SachinKonan/DopplerLifeDetectionSystem/main/CancellationCode/CancelGraph2/F3d.png

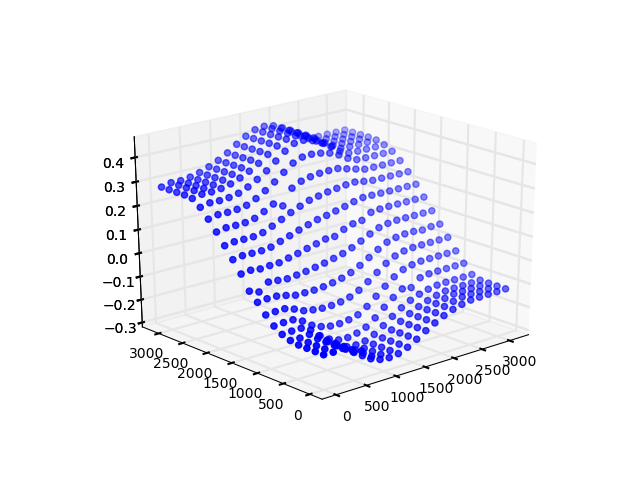
main/CancellationCode/CancelGraph2/F3d.png
