SachinKonan/DopplerLifeDetectionSystem/main/CancellationCode/CancelGraph2/phasepri.png

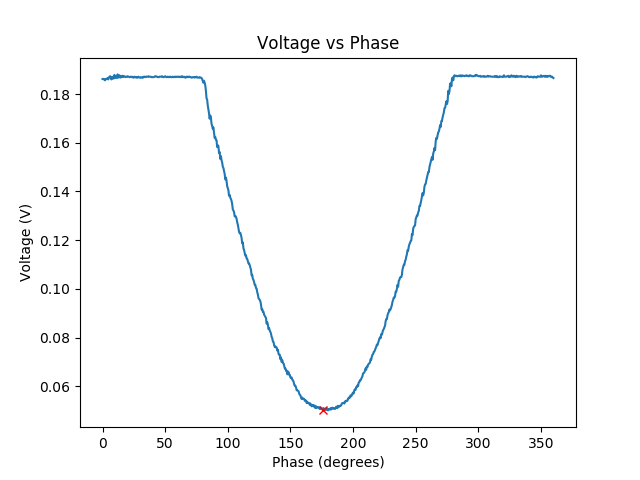
main/CancellationCode/CancelGraph2/phasepri.png
