SachinKonan/DopplerLifeDetectionSystem/main/CancellationCode/CancelGraph2/voltage.png

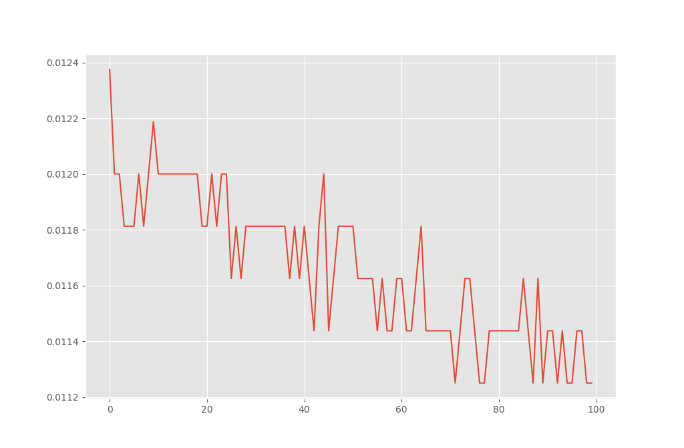
main/CancellationCode/CancelGraph2/voltage.png
