SachinKonan/DopplerLifeDetectionSystem/main/CancellationCode/CancelGraph2/voltampbrick.png

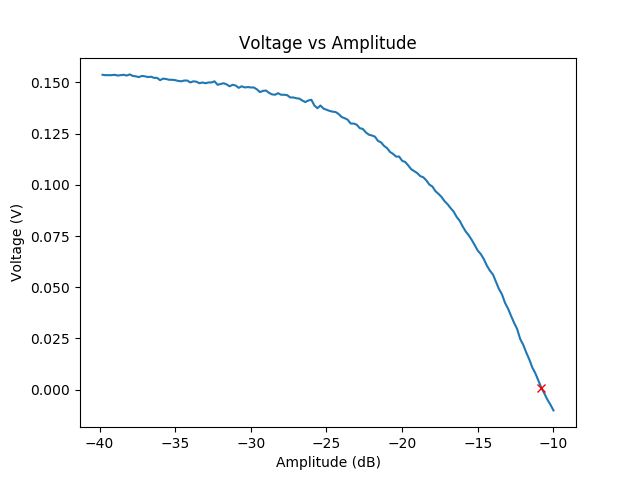
main/CancellationCode/CancelGraph2/voltampbrick.png
