SachinKonan/DopplerLifeDetectionSystem/main/CancellationCode/CancelGraph2/voltphastg.png

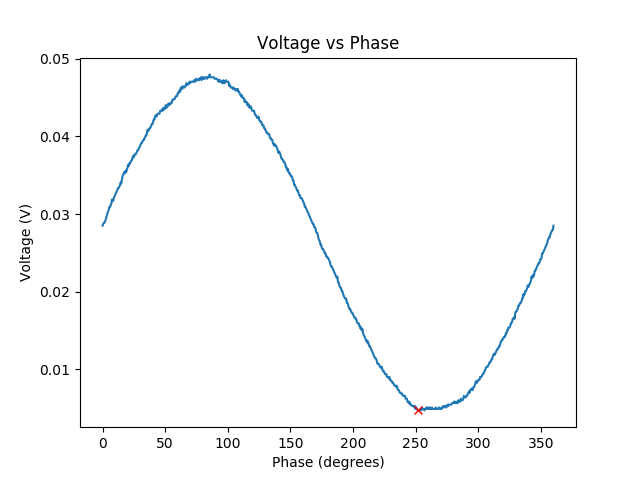
main/CancellationCode/CancelGraph2/voltphastg.png
