SachinKonan/DopplerLifeDetectionSystem/main/CancellationCode/CancelGraph2/voltvsamp3dB.png

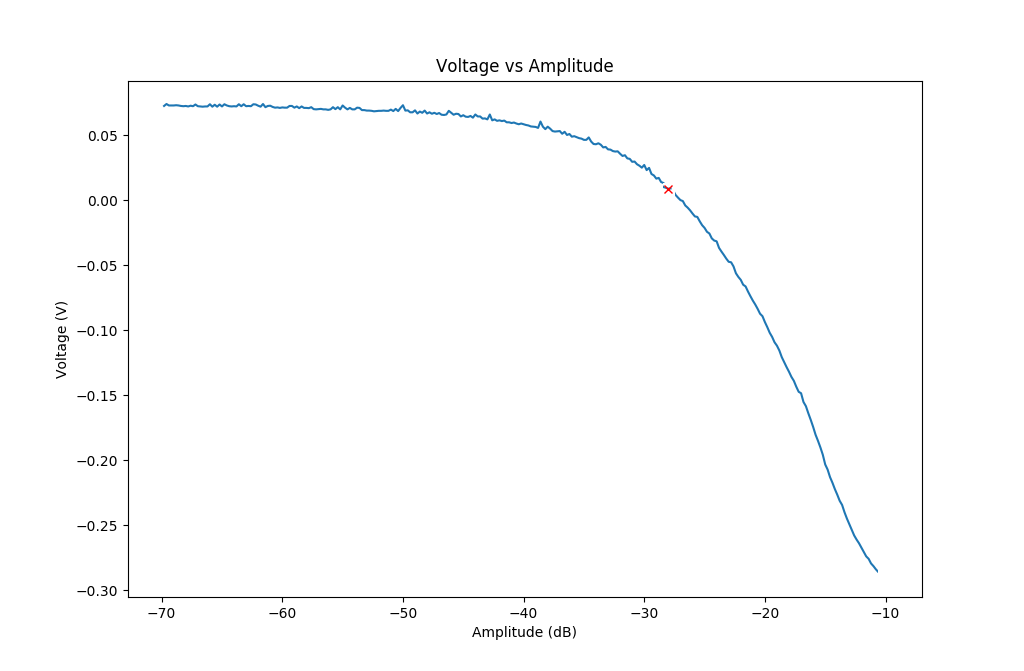
main/CancellationCode/CancelGraph2/voltvsamp3dB.png
