SachinKonan/DopplerLifeDetectionSystem/main/CancellationCode/CancelGraph2/voltvsamp30dB.png

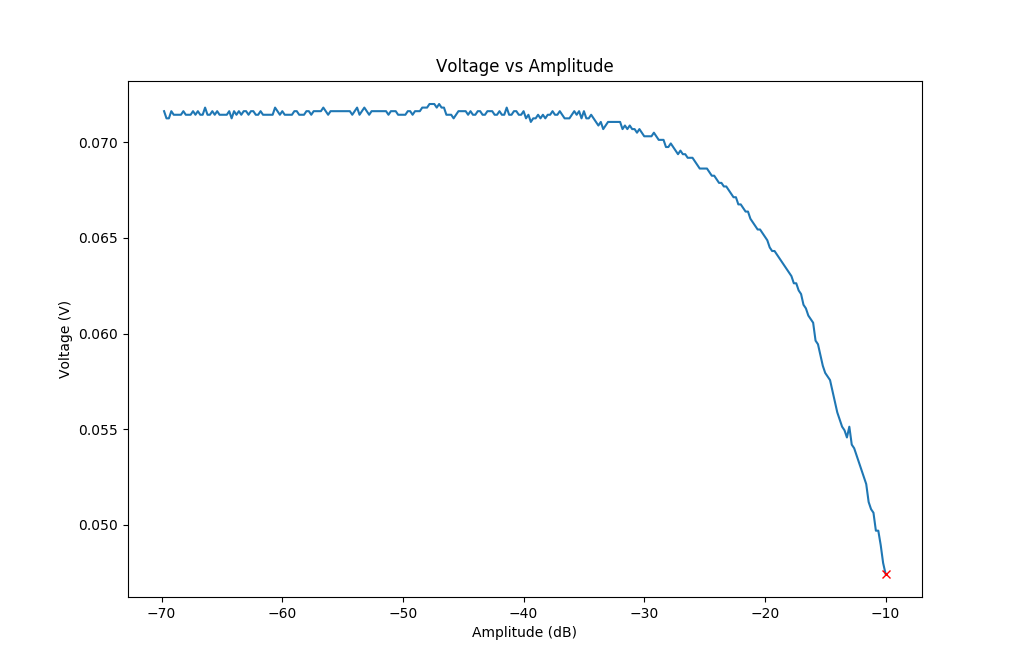
main/CancellationCode/CancelGraph2/voltvsamp30dB.png
