SachinKonan/DopplerLifeDetectionSystem/main/CancellationCode/CancelGraph2/voltvsamp130.png

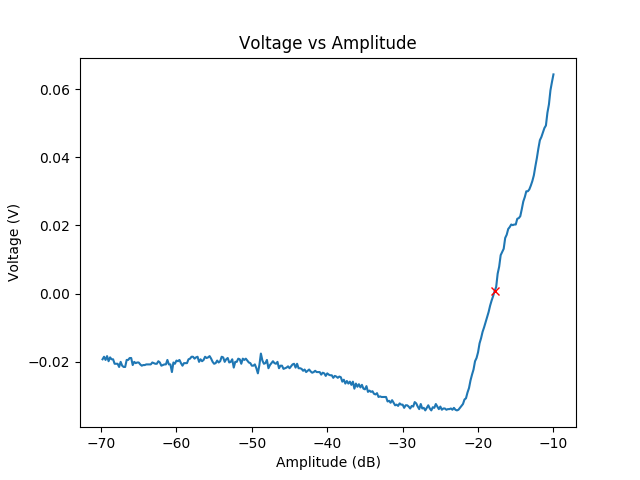
main/CancellationCode/CancelGraph2/voltvsamp130.png
