SachinKonan/DopplerLifeDetectionSystem/main/CancellationCode/CancelGraph2/voltvsampconcrete1.png

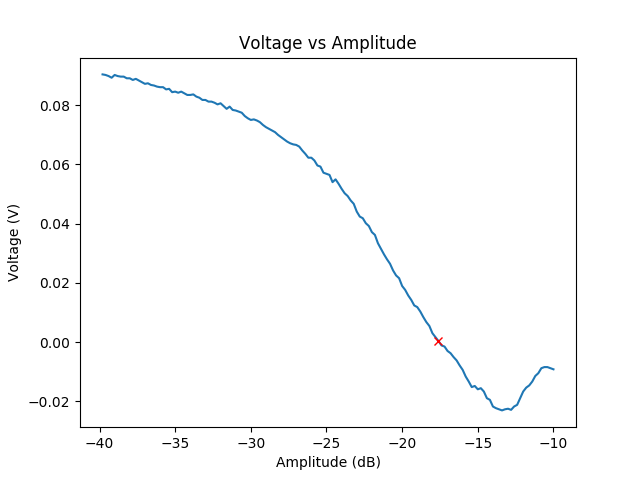
main/CancellationCode/CancelGraph2/voltvsampconcrete1.png
