SachinKonan/DopplerLifeDetectionSystem/main/CancellationCode/CancelGraph2/voltvsampnotten.png

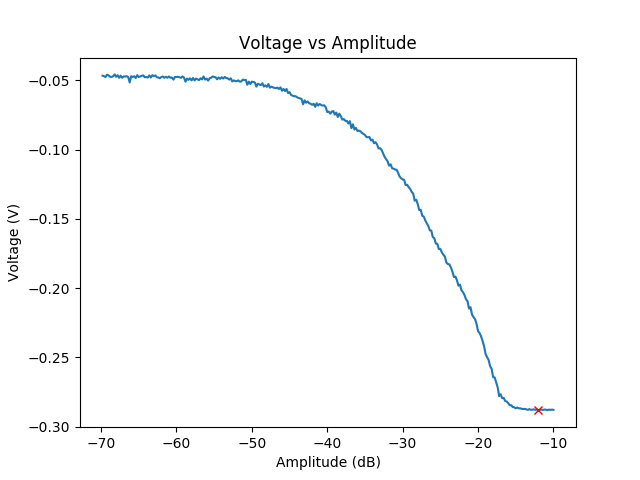
main/CancellationCode/CancelGraph2/voltvsampnotten.png
