SachinKonan/DopplerLifeDetectionSystem/main/CancellationCode/CancelGraph2/voltvsphase3dB.png

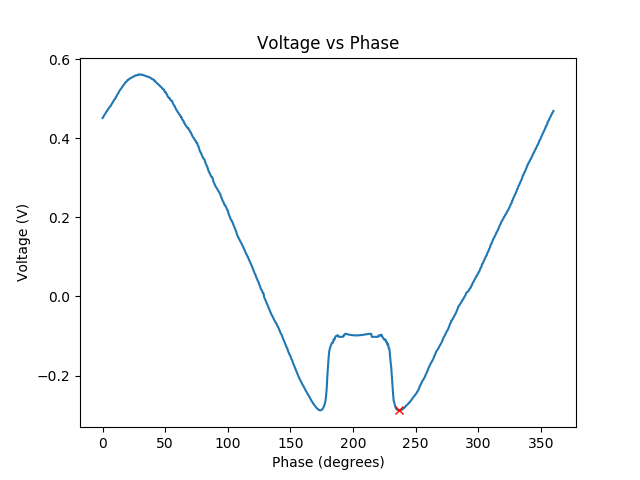
main/CancellationCode/CancelGraph2/voltvsphase3dB.png
