SachinKonan/DopplerLifeDetectionSystem/main/CancellationCode/CancelGraph2/voltvsphase30dB.png

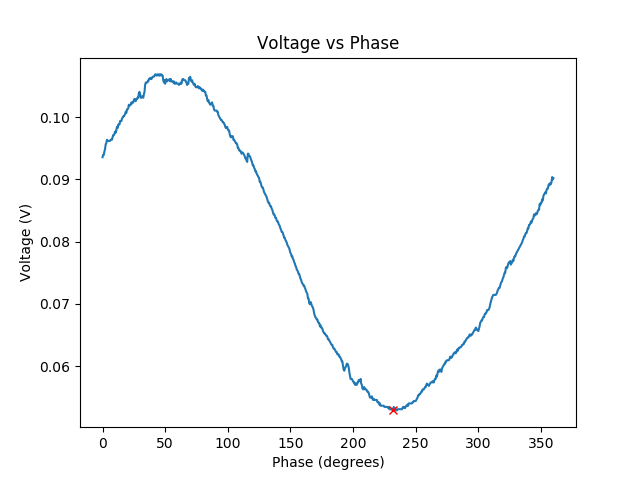
main/CancellationCode/CancelGraph2/voltvsphase30dB.png
