SachinKonan/DopplerLifeDetectionSystem/main/CancellationCode/CancelGraph2/voltvsphase130.png

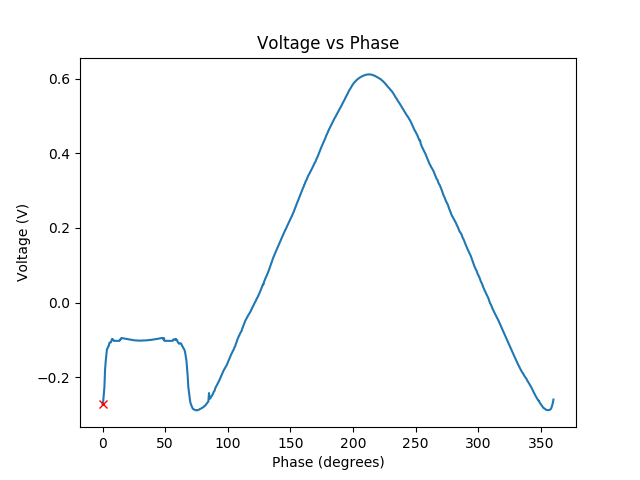
main/CancellationCode/CancelGraph2/voltvsphase130.png
