SachinKonan/DopplerLifeDetectionSystem/main/CancellationCode/CancelGraph2/voltvsphaseconcrete1.png

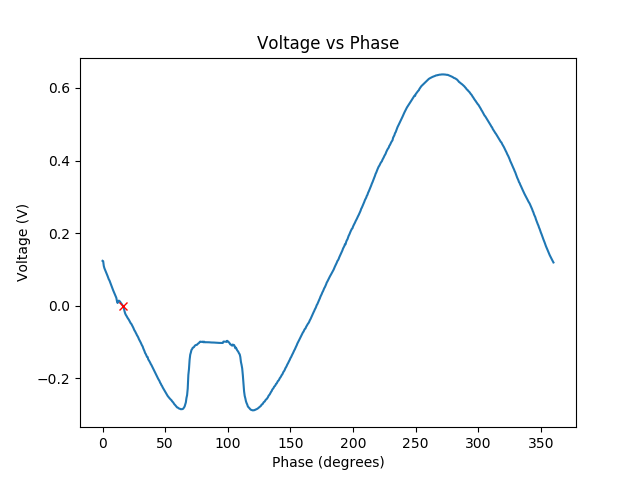
main/CancellationCode/CancelGraph2/voltvsphaseconcrete1.png
