SachinKonan/DopplerLifeDetectionSystem/main/CancellationCode/CancelGraph2/voltvsphasenoatten.png

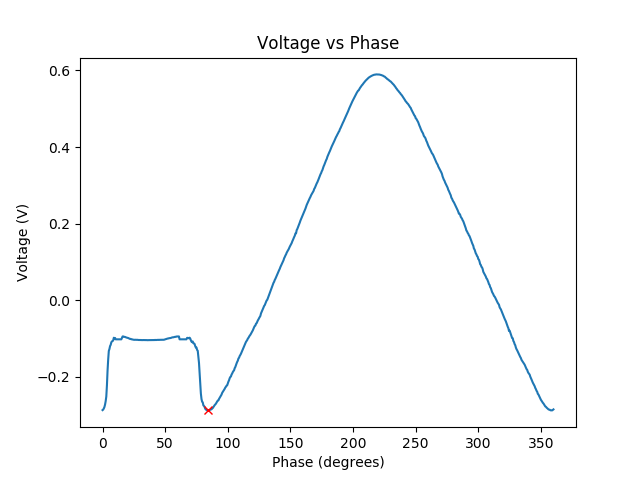
main/CancellationCode/CancelGraph2/voltvsphasenoatten.png
