SachinKonan/DopplerLifeDetectionSystem/main/CancellationCode/phasecalib.png

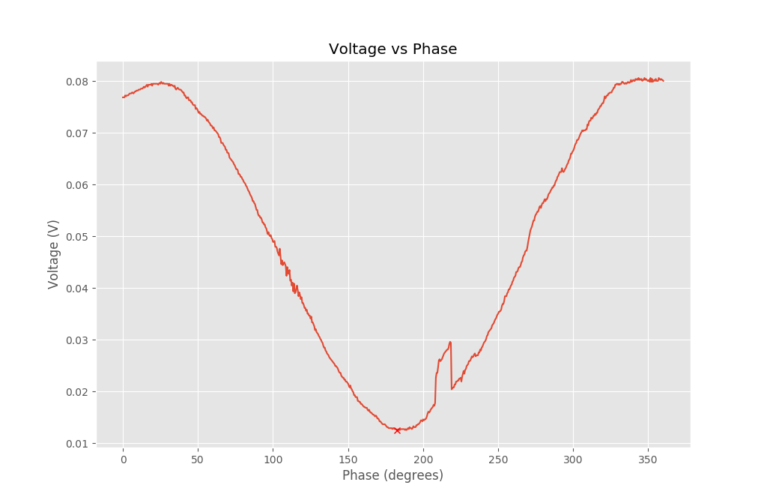
main/CancellationCode/phasecalib.png
