SachinKonan/DopplerLifeDetectionSystem/main/SimpleOscilloscope/RPIVisulaization.png

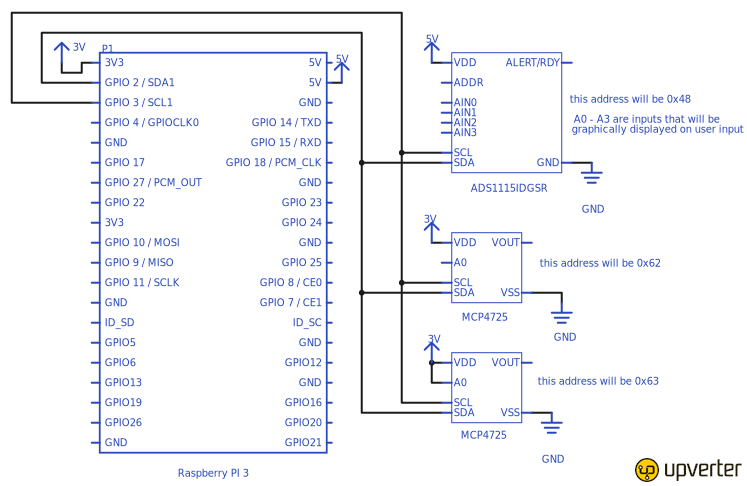
main/SimpleOscilloscope/RPIVisulaization.png
