SachinKonan/DopplerLifeDetectionSystem/PCBRadar/radarpcb3D.png

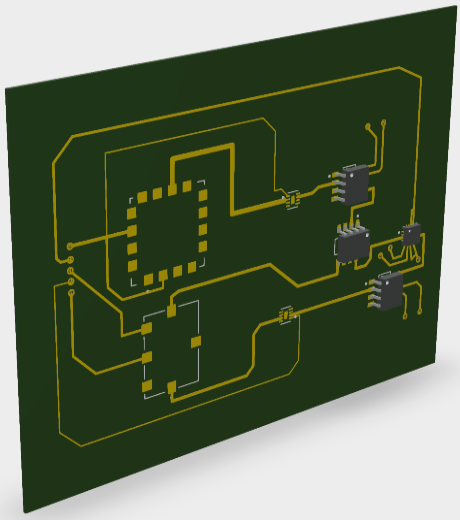
PCBRadar/radarpcb3D.png
