SachinKonan/DopplerLifeDetectionSystem/PCBRadar/radarpcb.PNG

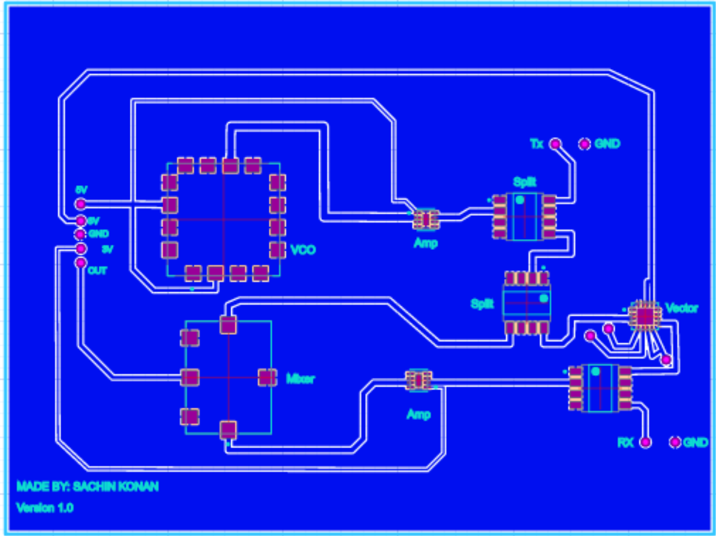
PCBRadar/radarpcb.PNG
