SachinKonan/DopplerLifeDetectionSystem/RadarFull/antennaplacement.png

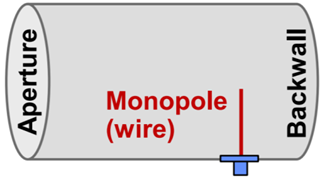
RadarFull/antennaplacement.png
