SachinKonan/DopplerLifeDetectionSystem/RadarFull/filter.amplifier.circuit.png

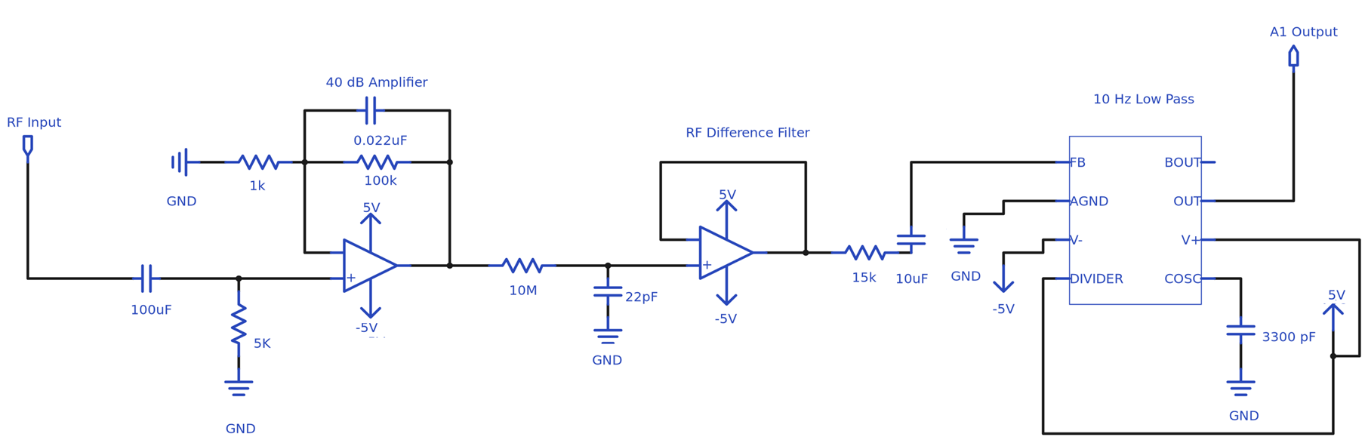
RadarFull/filter.amplifier.circuit.png
