SachinKonan/DopplerLifeDetectionSystem/RadarFull/powersupply.png

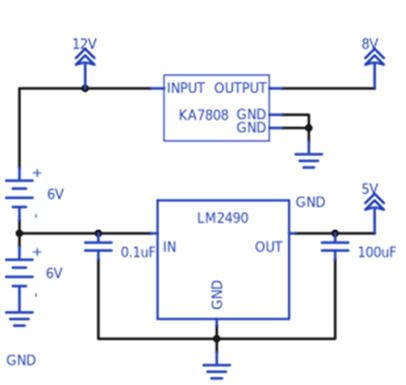
RadarFull/powersupply.png
