SachinKonan/DopplerLifeDetectionSystem/RadarFull/radarfull.png

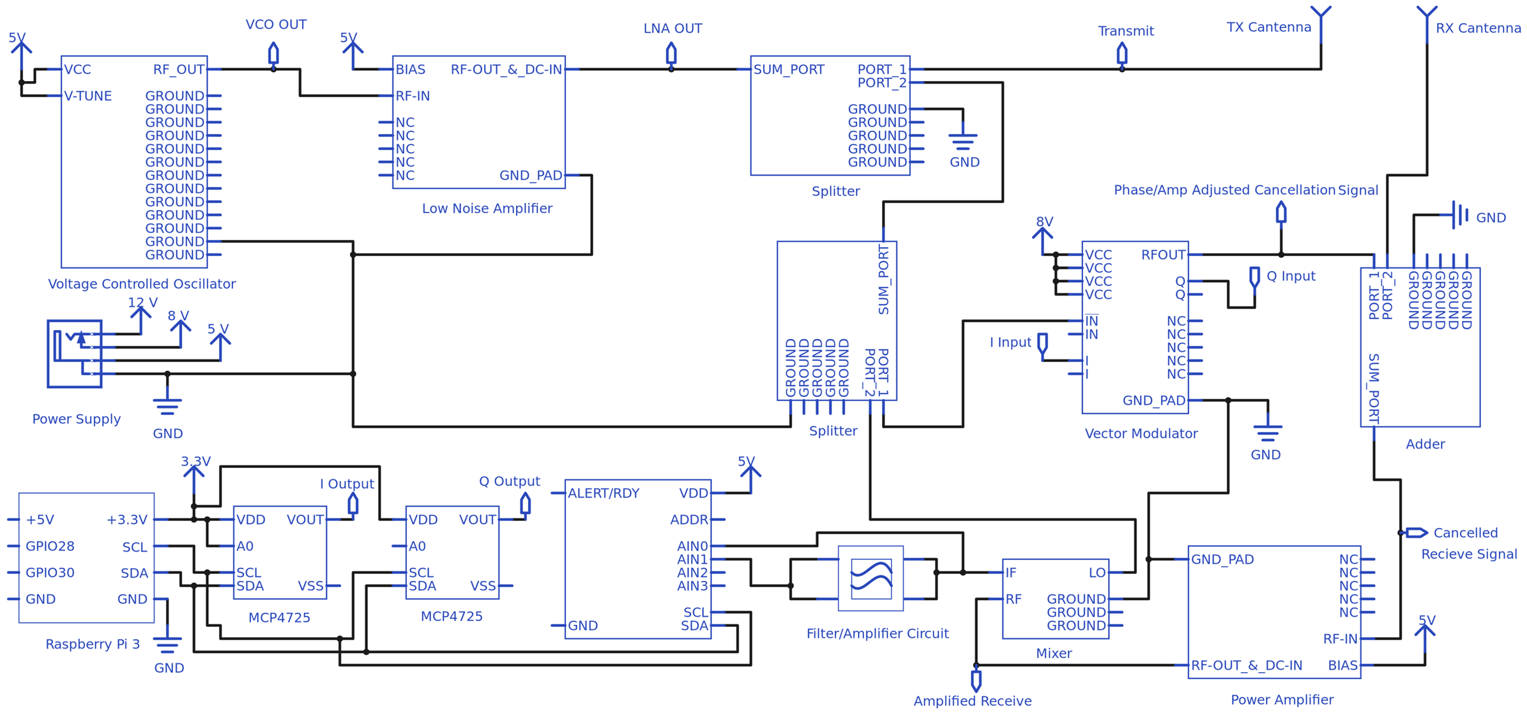
RadarFull/radarfull.png
