SachinKonan/DopplerLifeDetectionSystem/main/CancellationCode/CalibrationGraphs/control.png

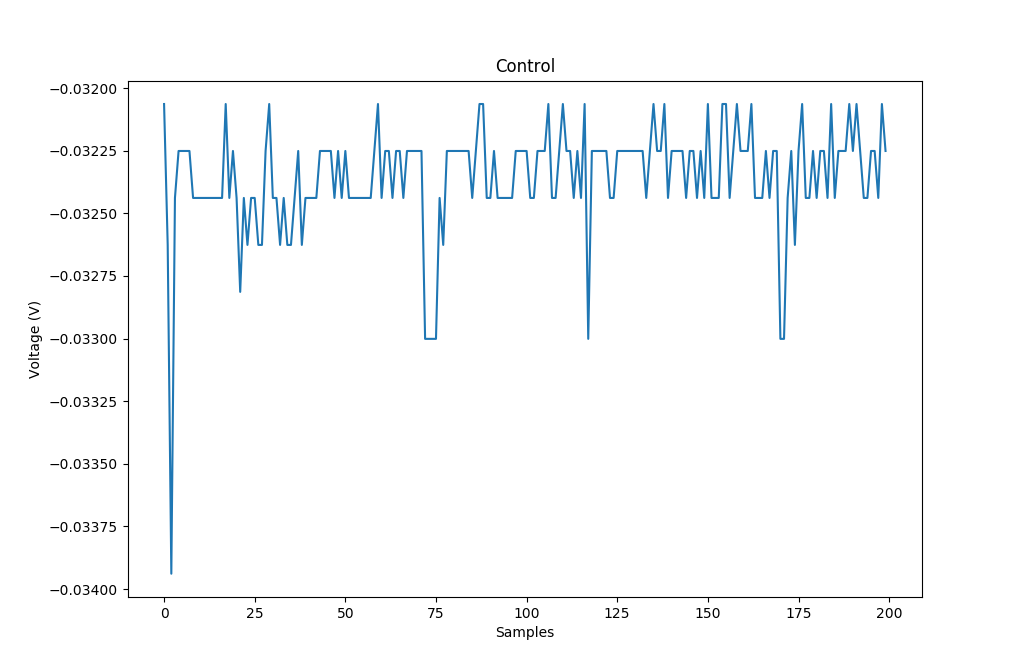
main/CancellationCode/CalibrationGraphs/control.png
