SachinKonan/DopplerLifeDetectionSystem/main/CancellationCode/CalibrationGraphs/voltvsamp1.png

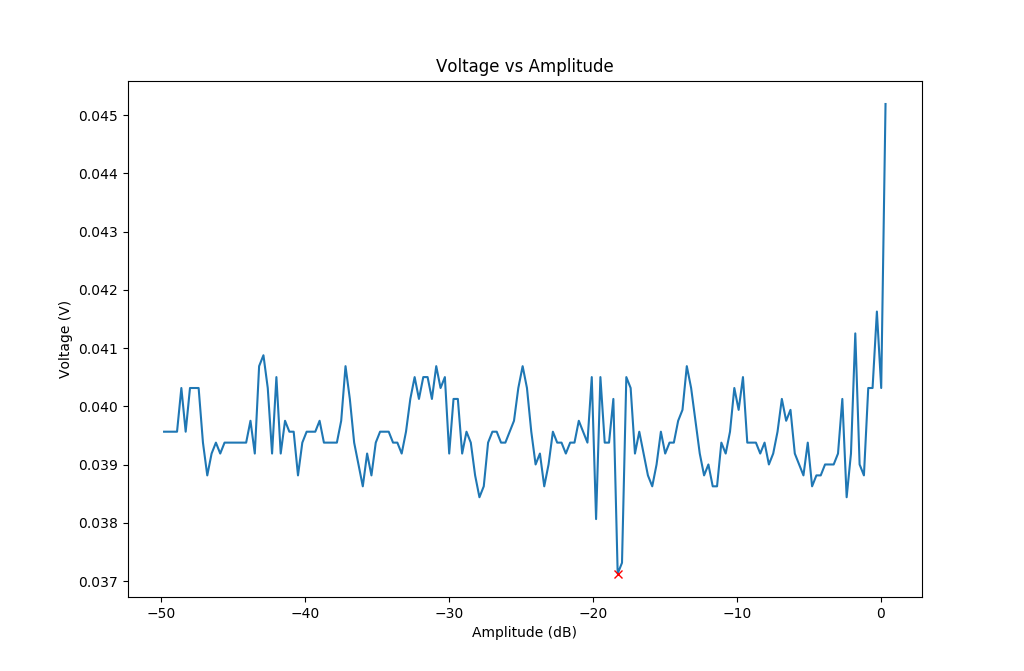
main/CancellationCode/CalibrationGraphs/voltvsamp1.png
