SachinKonan/DopplerLifeDetectionSystem/main/CancellationCode/CalibrationGraphs/voltvsamp2.png

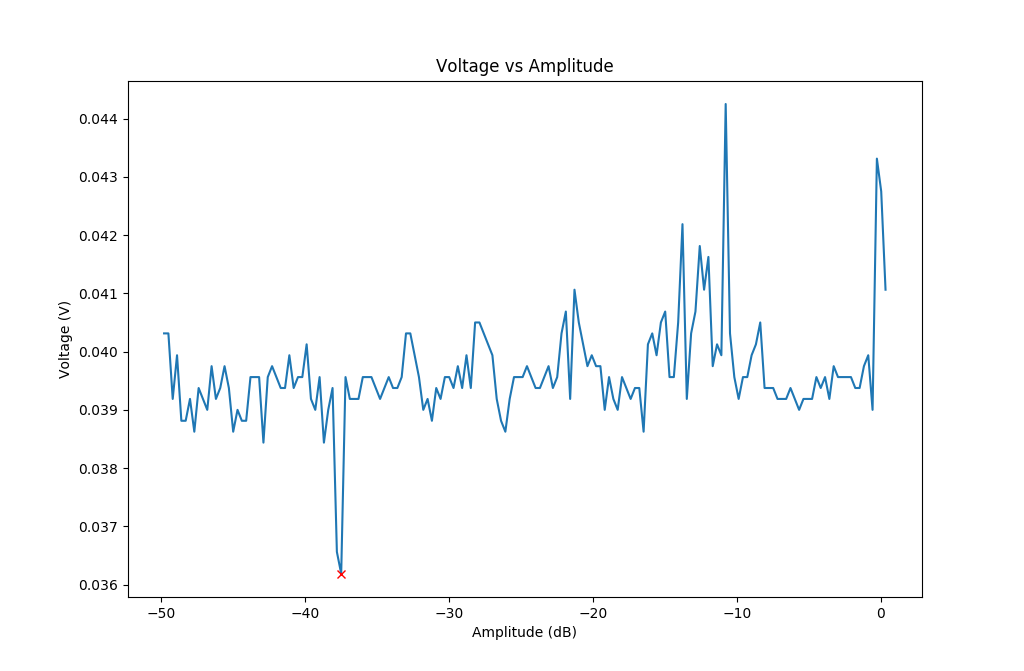
main/CancellationCode/CalibrationGraphs/voltvsamp2.png
