SachinKonan/DopplerLifeDetectionSystem/main/CancellationCode/CalibrationGraphs/voltvsamp3.png

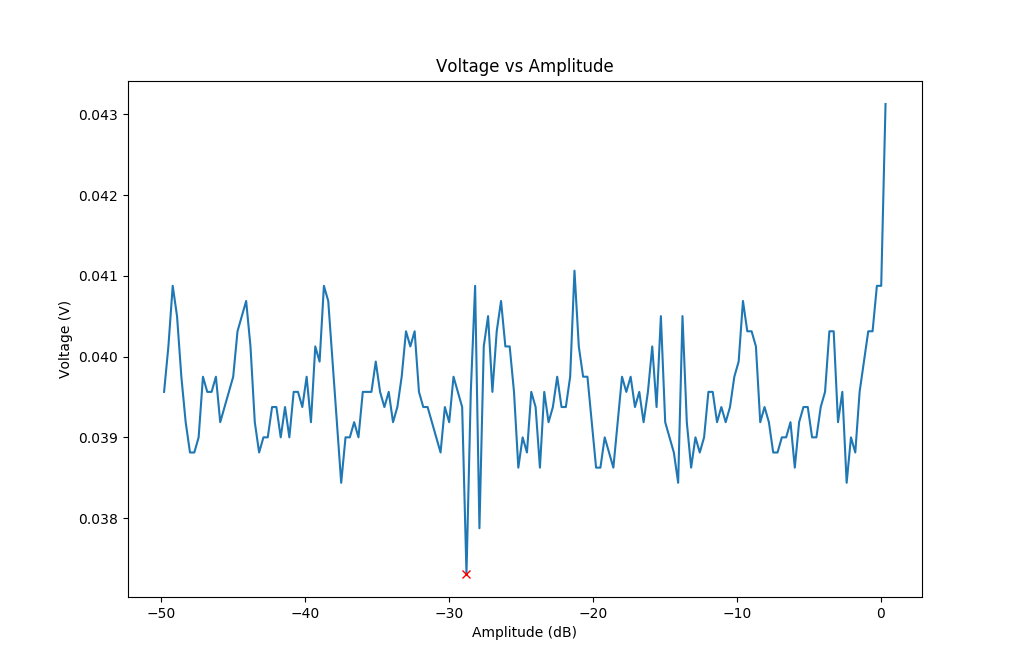
main/CancellationCode/CalibrationGraphs/voltvsamp3.png
