SachinKonan/DopplerLifeDetectionSystem/main/CancellationCode/CalibrationGraphs/voltvsamp4.png

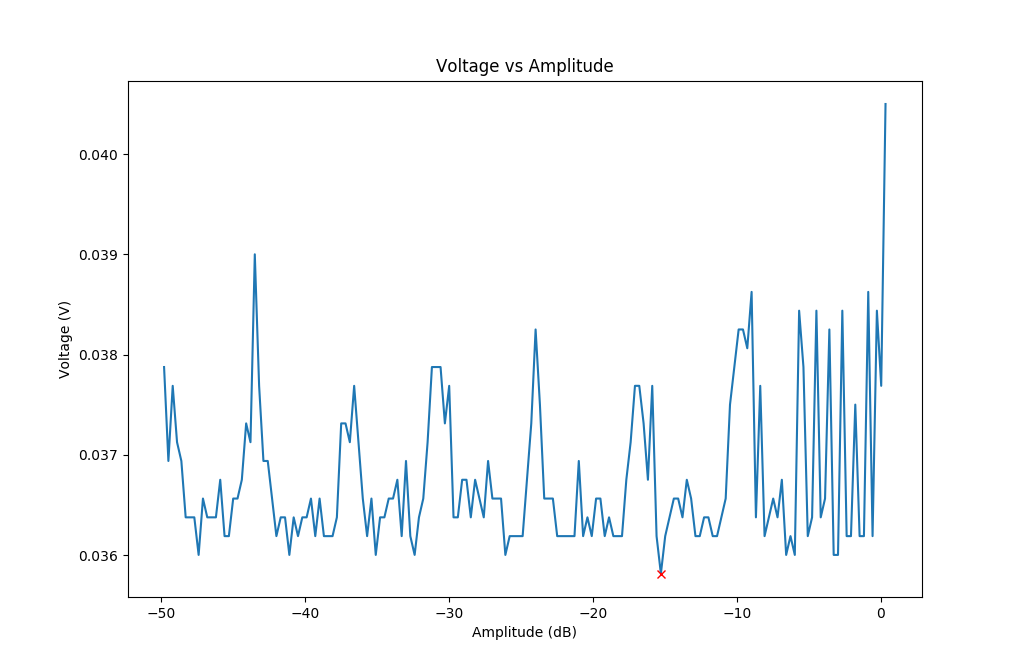
main/CancellationCode/CalibrationGraphs/voltvsamp4.png
