SachinKonan/DopplerLifeDetectionSystem/main/CancellationCode/CalibrationGraphs/voltvsamp5.png

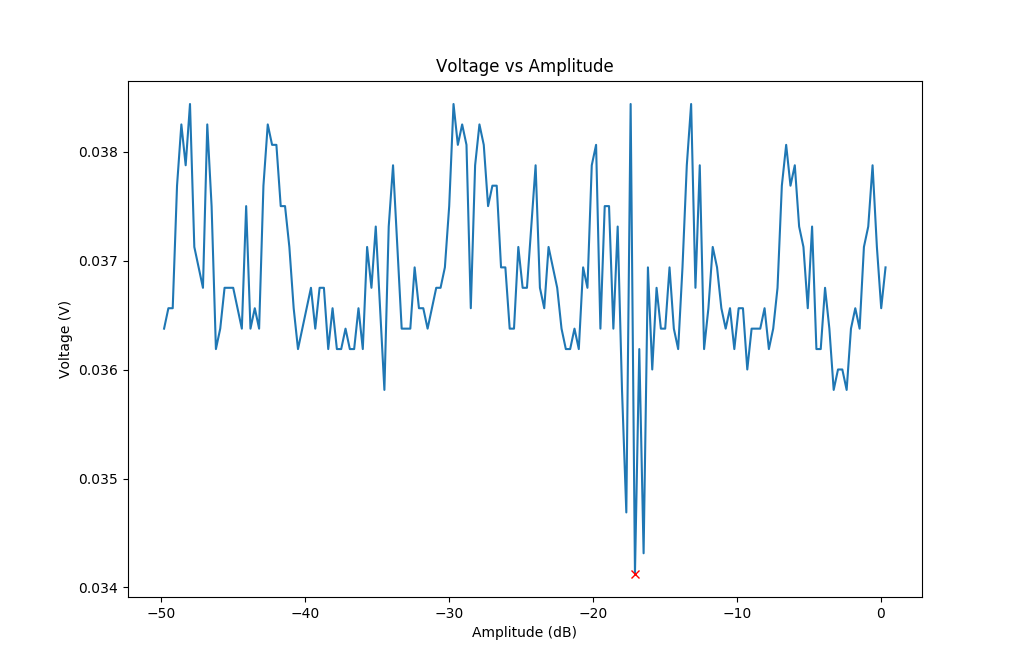
main/CancellationCode/CalibrationGraphs/voltvsamp5.png
