SachinKonan/DopplerLifeDetectionSystem/main/CancellationCode/CalibrationGraphs/voltvsamp.png

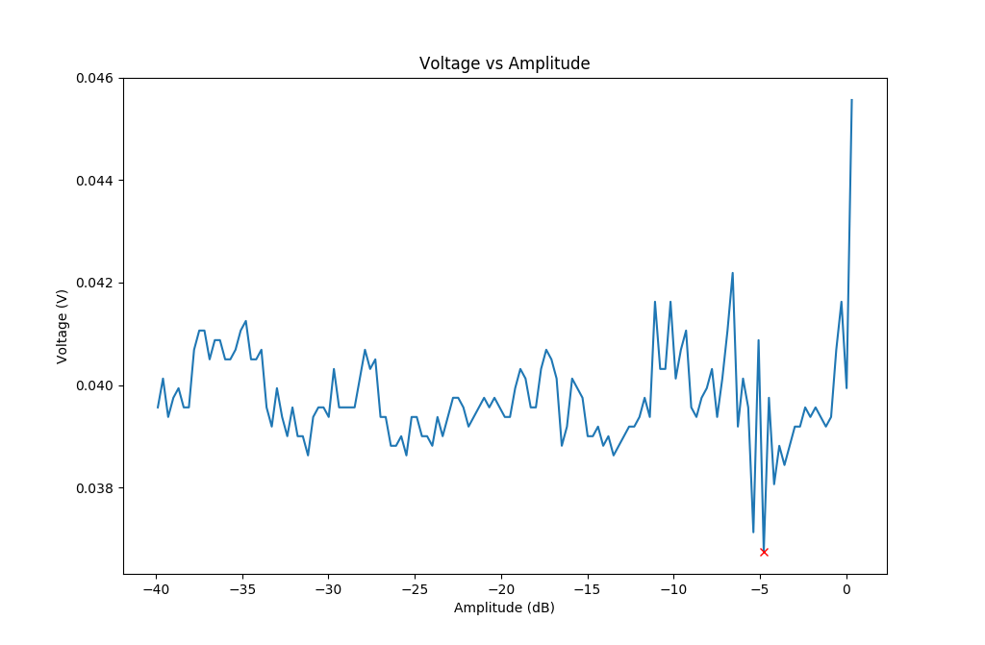
main/CancellationCode/CalibrationGraphs/voltvsamp.png
