SachinKonan/DopplerLifeDetectionSystem/main/CancellationCode/CalibrationGraphs/voltvsamprevisedphase.png

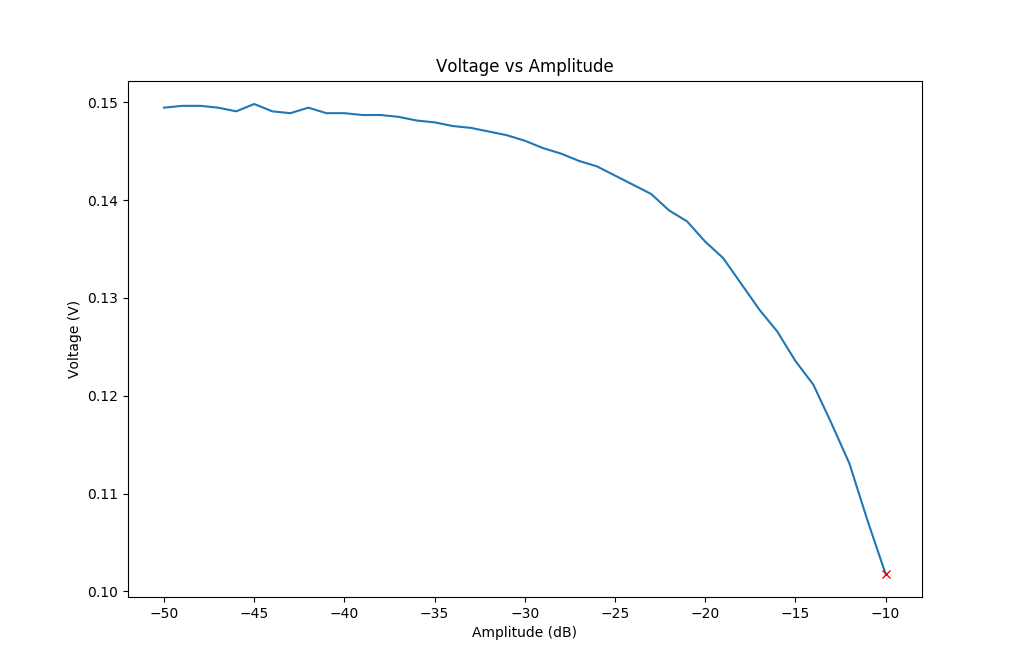
main/CancellationCode/CalibrationGraphs/voltvsamprevisedphase.png
