SachinKonan/DopplerLifeDetectionSystem/main/CancellationCode/CalibrationGraphs/voltvsphase1.png

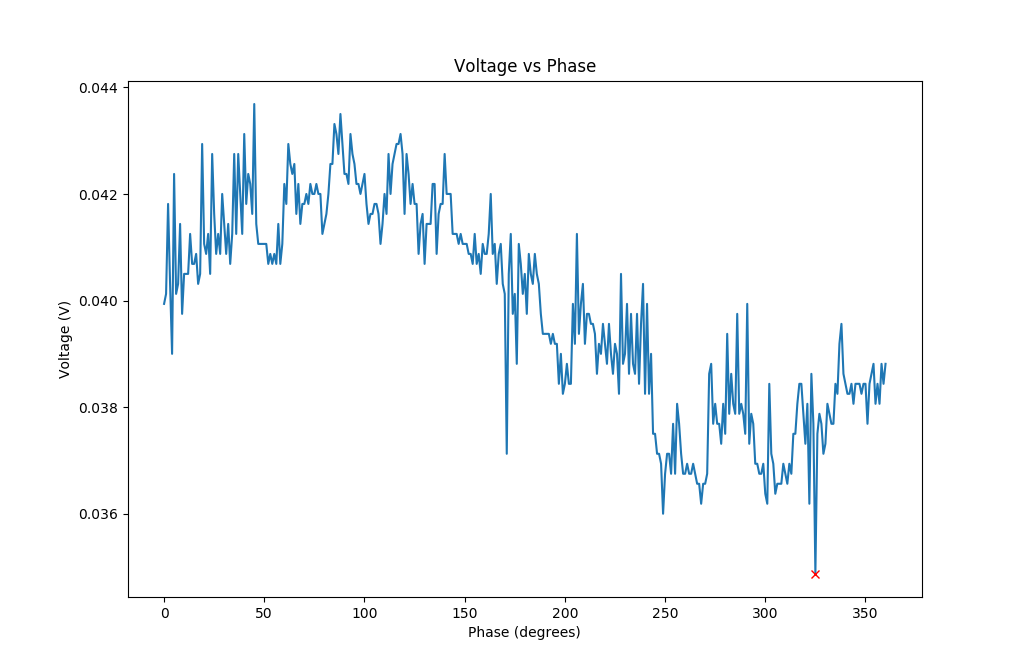
main/CancellationCode/CalibrationGraphs/voltvsphase1.png
