SachinKonan/DopplerLifeDetectionSystem/main/CancellationCode/CalibrationGraphs/voltvsphase2.png

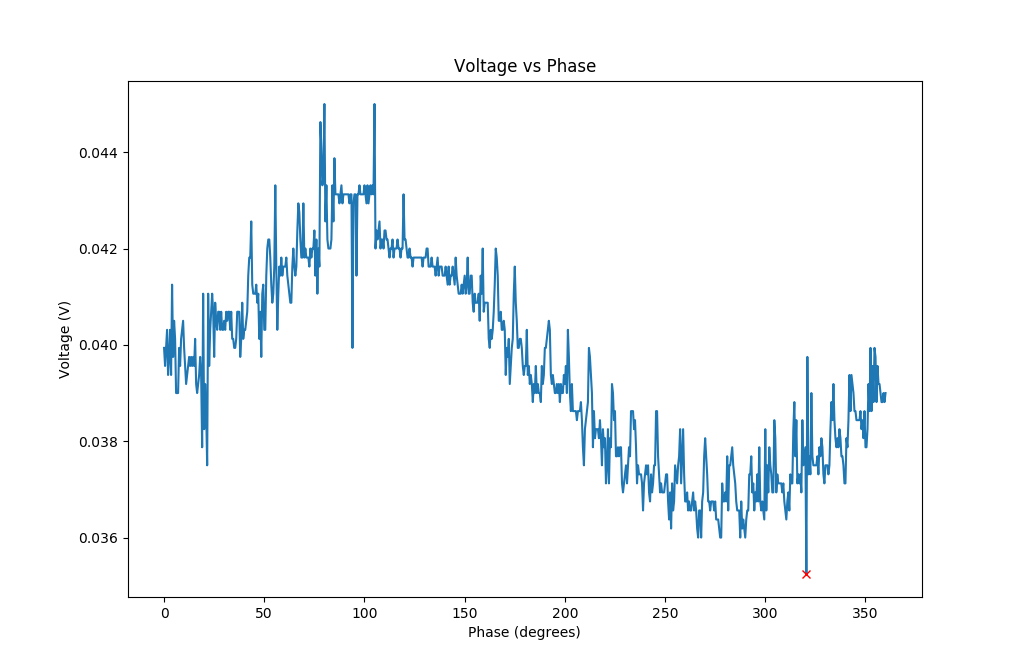
main/CancellationCode/CalibrationGraphs/voltvsphase2.png
