SachinKonan/DopplerLifeDetectionSystem/main/CancellationCode/CalibrationGraphs/voltvsphase3.png

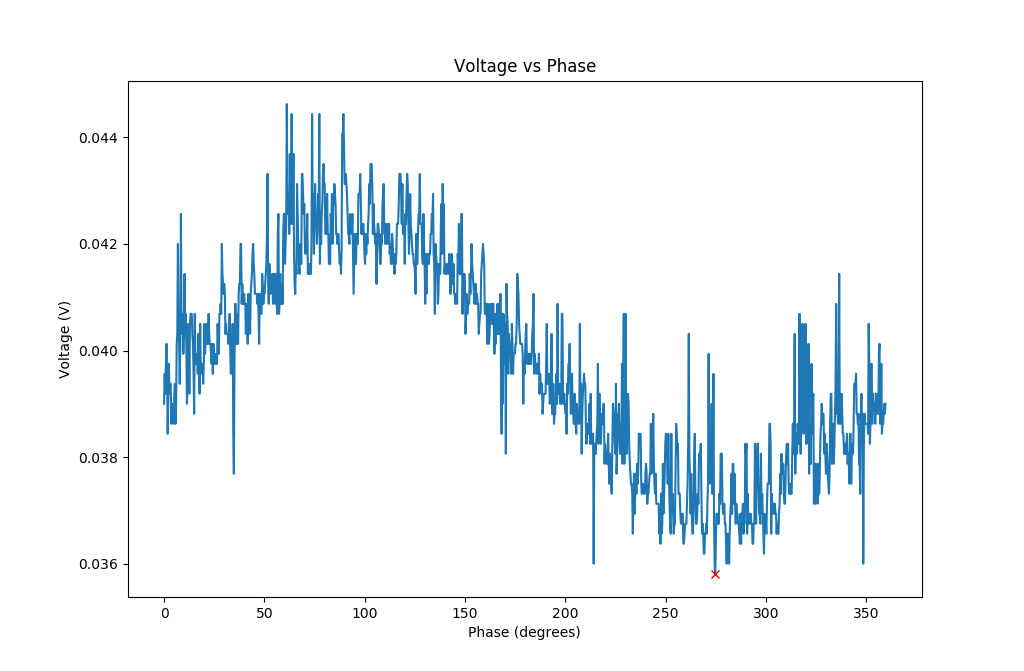
main/CancellationCode/CalibrationGraphs/voltvsphase3.png
