SachinKonan/DopplerLifeDetectionSystem/main/CancellationCode/CalibrationGraphs/voltvsphase7.png

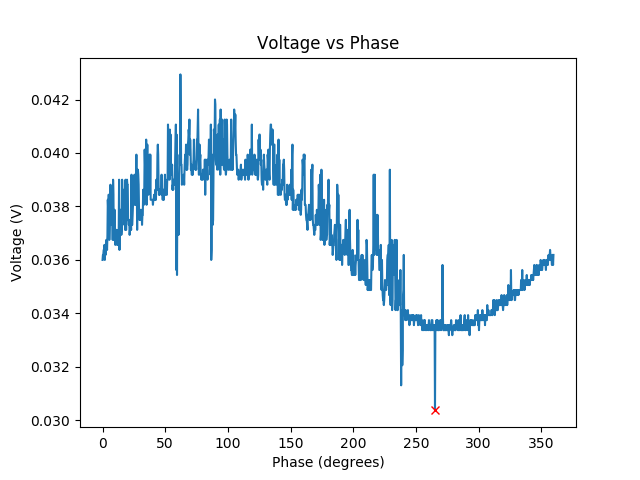
main/CancellationCode/CalibrationGraphs/voltvsphase7.png
