SachinKonan/DopplerLifeDetectionSystem/main/CancellationCode/CalibrationGraphs/voltvsphase8.png

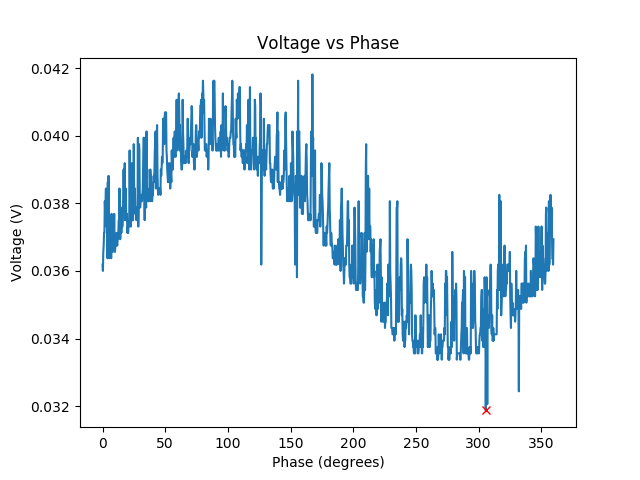
main/CancellationCode/CalibrationGraphs/voltvsphase8.png
