SachinKonan/DopplerLifeDetectionSystem/main/CancellationCode/CalibrationGraphs/voltvsphase720.png

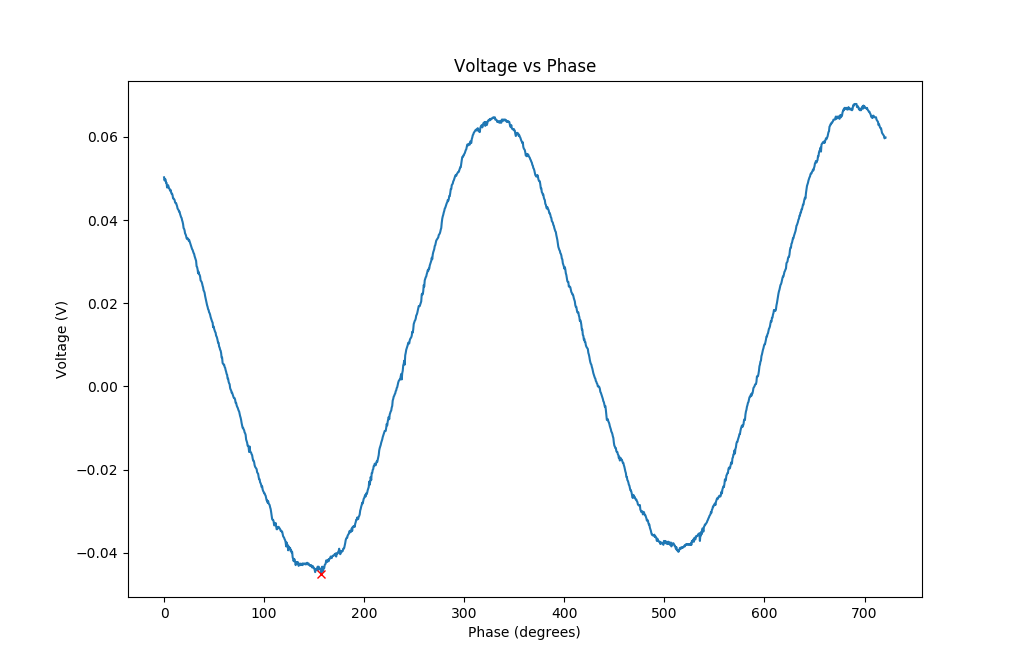
main/CancellationCode/CalibrationGraphs/voltvsphase720.png
