SachinKonan/DopplerLifeDetectionSystem/main/CancellationCode/CalibrationGraphs/voltvsphaserevised1.png

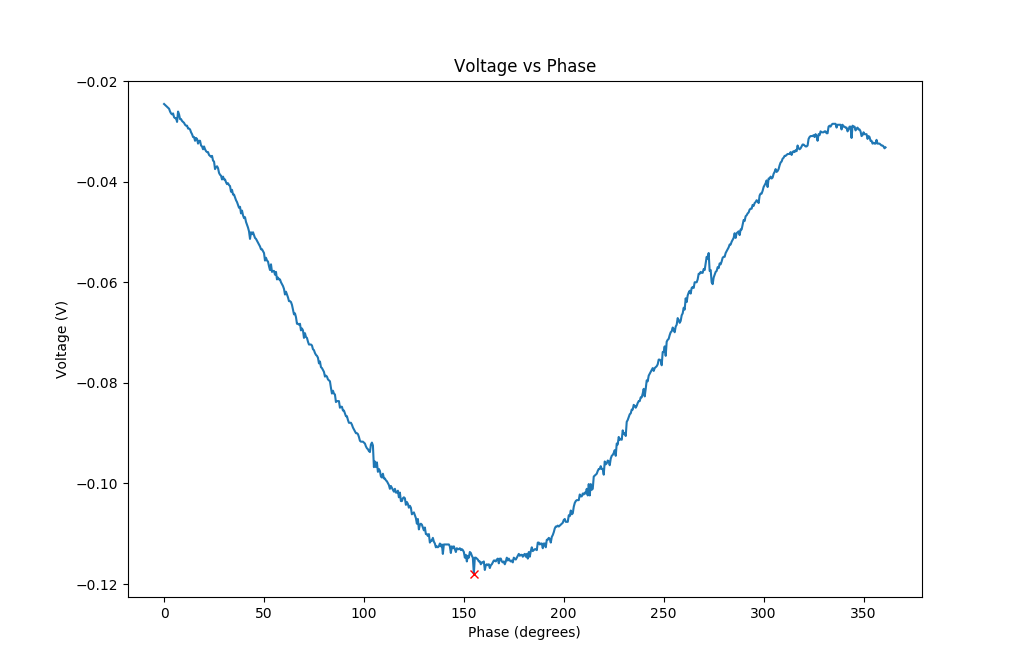
main/CancellationCode/CalibrationGraphs/voltvsphaserevised1.png
