SachinKonan/DopplerLifeDetectionSystem/main/CancellationCode/CalibrationGraphs/voltvsratio.png

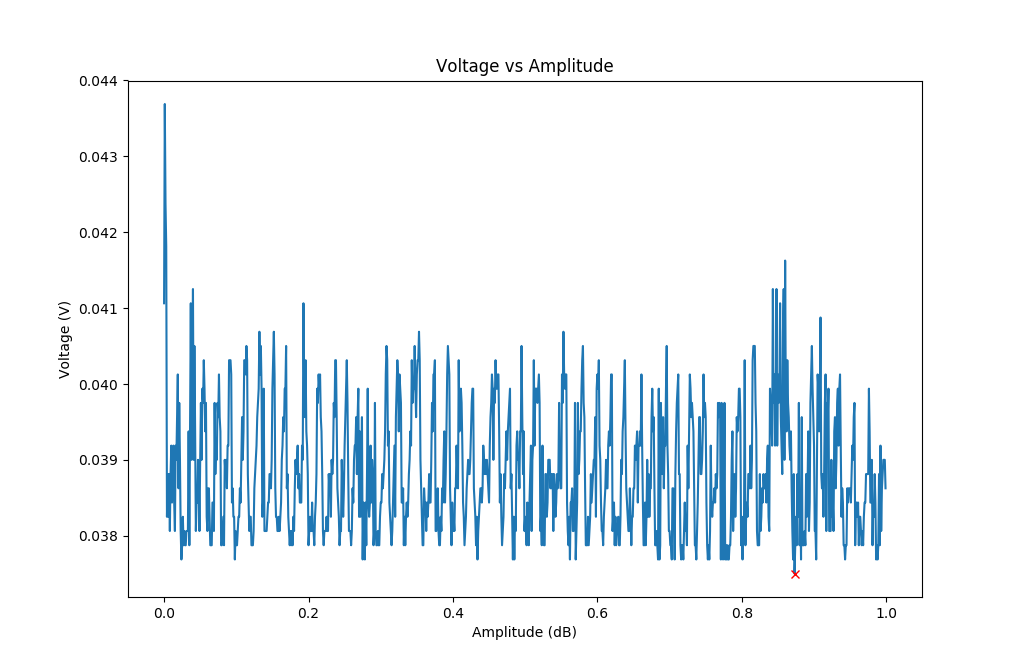
main/CancellationCode/CalibrationGraphs/voltvsratio.png
