SachinKonan/DopplerLifeDetectionSystem/SpiceCircuits/2ndOrderLowPass.asc

C1: cap; 330µ
C2: cap; 33µ
R1: res; 316
R2: res; 3520
R3: res; 1000
R4: res; 10000
U1: OP07
V1: voltage; ""; AC 1 0
V2: voltage; 5
V3: voltage; 5
Named nets: 0
.ac dec 20 0.1 100k
