SachinKonan/DopplerLifeDetectionSystem/SpiceCircuits/300kLowPass.asc

C1: cap; 1.5n
R1: res; 330
U1: LTC1052
V1: voltage; 5
V2: voltage; ""; AC 1 0
Named nets: 0
.ac dec 20 0.1 500k
