SachinKonan/DopplerLifeDetectionSystem/SpiceCircuits/DACLowPass.asc

C1: cap; 10µ
R1: res; 8.2k
V1: voltage; ""; AC 1 0
Named nets: 0
.ac dec 20 0.1 100000000
