SachinKonan/DopplerLifeDetectionSystem/SpiceCircuits/10HzLowPass.asc

C1: cap; 10µ
R1: res; 1.5k
U1: LTC1052
V1: voltage; 5
V2: voltage; ""; AC 1 0
Named nets: 0
.ac dec 20 0.1 100k
