SachinKonan/DopplerLifeDetectionSystem/SpiceCircuits/40dB Amplifier.asc

C1: cap; 100µ
C2: cap; 0.22µ
R1: res; 10k
R2: res; 100k
R3: res; 1k
U2: LTC1052
V1: voltage; ""; AC 1m 0
V2: voltage; 5
V3: voltage; 5
Named nets: 0
.ac dec 2 0.1 100
