SachinKonan/DopplerLifeDetectionSystem/SpiceCircuits/Draft4.asc

C1: cap; 2µ
C2: cap; 2µ
R1: res; 1k
R2: res; 1k
R3: res; 10k
R4: res; 10k
U1: LTC1052
V1: voltage; ""; AC 1 0
V2: voltage; 5
Named nets: 0
.ac dec 20 0.1 100k
