SachinKonan/DopplerLifeDetectionSystem/SpiceCircuits/Invert-Amp.asc

R1: res; 1k
R2: res; 2k
U1: LTC1052
V1: voltage; 5
V2: voltage; ""; AC 1 0
V3: voltage; 5
Named nets: 0
.ac dec 20 0.1 1M
