SachinKonan/DopplerLifeDetectionSystem/SpiceCircuits/Non-invertAmp.asc

R1: res; 2k
R2: res; 1k
U1: LTC1052
V1: voltage; 5
V2: voltage; ""; AC 1 0
Named nets: 0
.ac dec 20 0.1 1000000k
